wingsumlaw/nes-shortcut-keyboard/schematic/nes-keyboard.sch

## KiCad design schematic/nes-keyboard.sch (2022-07-04, an earlier design)

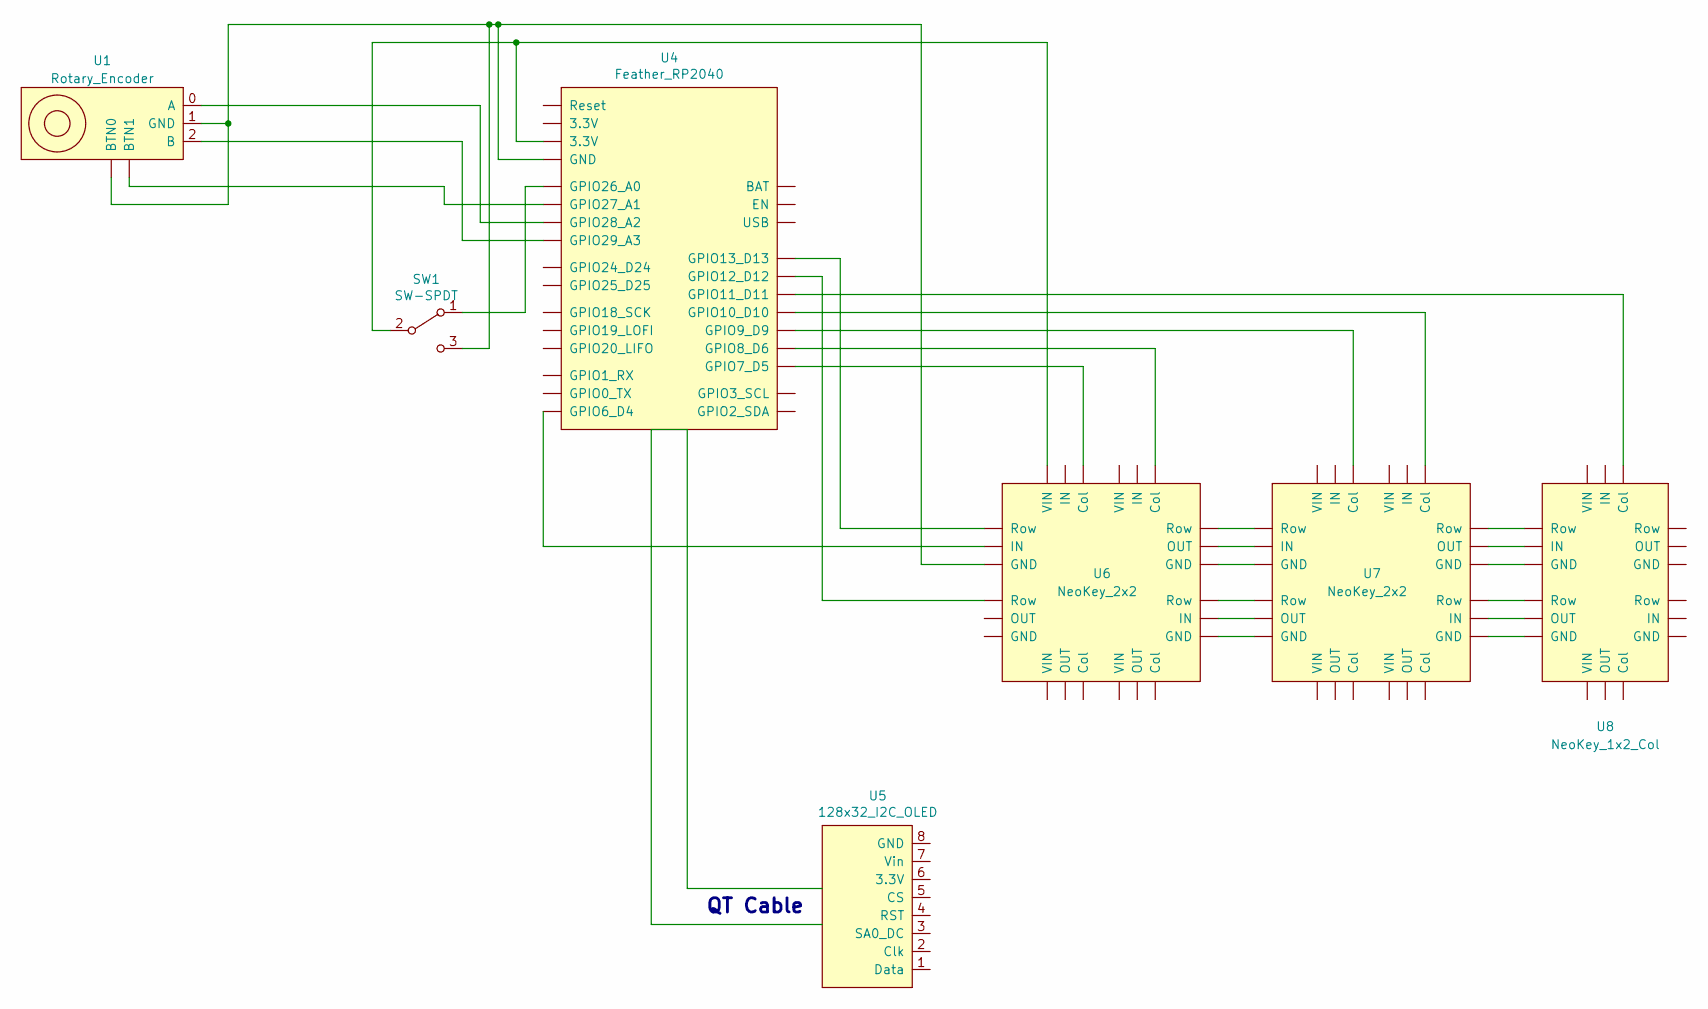
[picture p4: schematic nes-keyboard.sch]

Parts:
SW1: SW-SPDT
U1: Rotary_Encoder
U4: Feather_RP2040
U5: 128x32_I2C_OLED
U6, U7: NeoKey_2x2
U8: NeoKey_1x2_Col

Connections:
unnamed: SW1.1 (A), U4.~
unnamed: SW1.2 (B), U4.~, U6.~
unnamed: SW1.3 (C), U1.1 (GND), U1.~ (BTN0), U4.~, U6.~
unnamed: U1.0 (A), U4.~
unnamed: U1.2 (B), U4.~
unnamed: U1.~ (BTN0), U4.~
unnamed: U4.~, U6.~, U7.~, U8.~
unnamed: U6.~, U7.~
unnamed: U7.~, U8.~

Notes on the sheet:
QT Cable
